M0HID/Keyboard/pcb/CherryMX-master/r3/r3_200.STEP

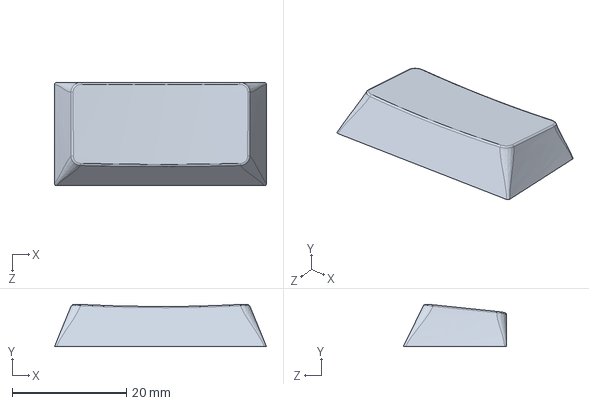
[picture p16: CAD file, 2025-07-31]
pcb/CherryMX-master/r3/r3_200.STEP
37.1 x 7.40 x 18.1 mm
