M0HID/Keyboard/pcb/CherryMX-master/r4/r4_225C.step

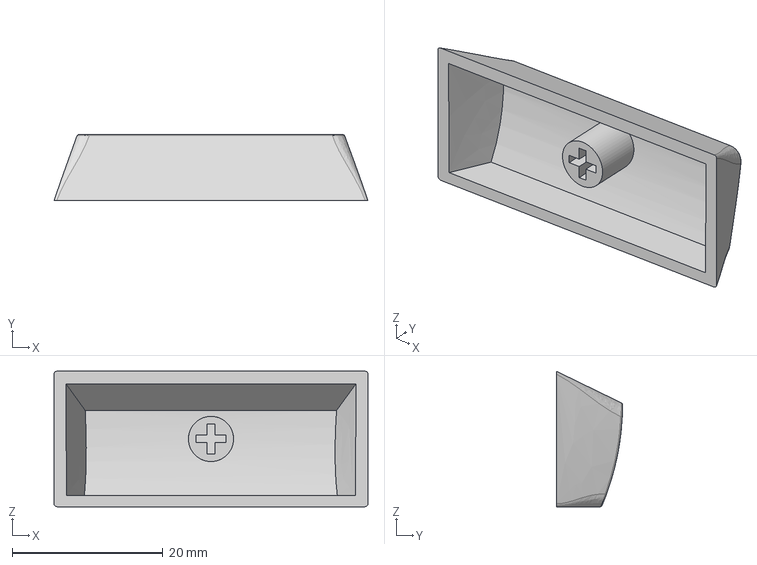
[picture p17: CAD file, 2025-07-31]
pcb/CherryMX-master/r4/r4_225C.step
41.7 x 8.80 x 18.0 mm
