M0HID/Keyboard/PROD/bottomshell.stl

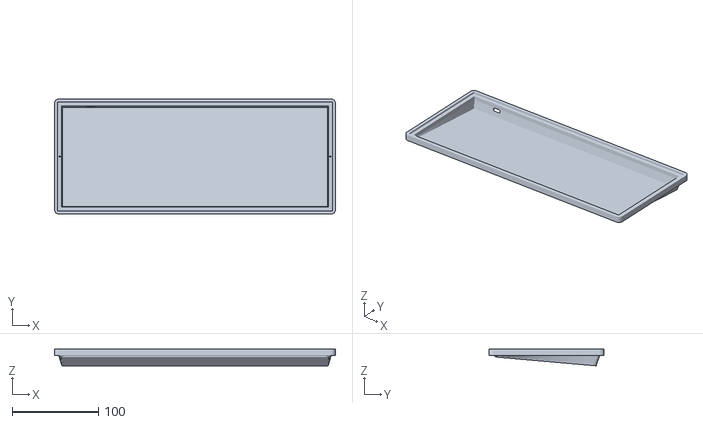
[picture p18: CAD file, 2025-07-31]
PROD/bottomshell.stl
326.0 x 133.6 x 19.4
