M0HID/Keyboard/pcb/CherryMX-master/r3/r3_150.STEP

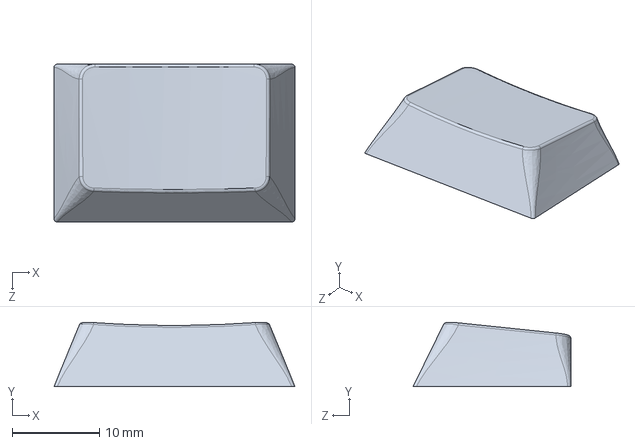
[picture p19: CAD file, 2025-07-31]
pcb/CherryMX-master/r3/r3_150.STEP
27.6 x 7.38 x 18.1 mm
