M0HID/Keyboard/pcb/CherryMX-master/r4/r4_100.STEP

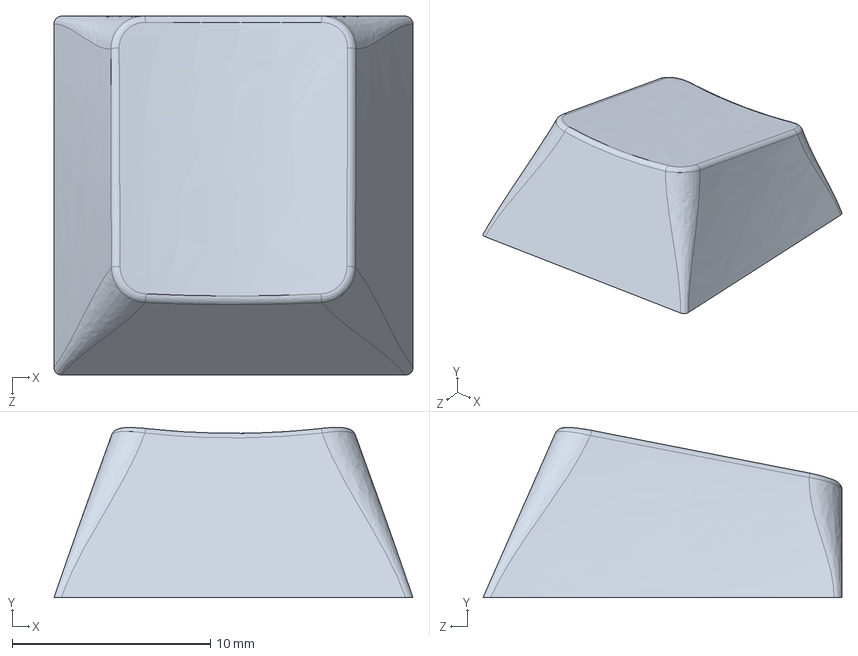
[picture p20: CAD file, 2025-07-31]
pcb/CherryMX-master/r4/r4_100.STEP
18.1 x 8.58 x 18.1 mm
