M0HID/Keyboard/pcb/CherryMX-master/r3/r3_100_sculpted.STEP

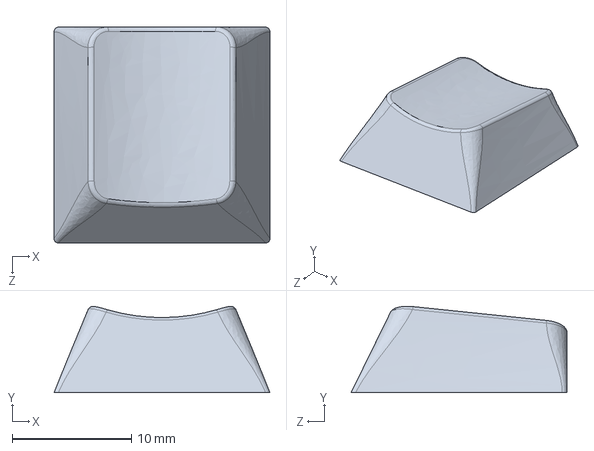
[picture p21: CAD file, 2025-07-31]
pcb/CherryMX-master/r3/r3_100_sculpted.STEP
18.1 x 7.24 x 18.1 mm
