M0HID/Keyboard/pcb/CherryMX-master/r4/r4_700.STEP

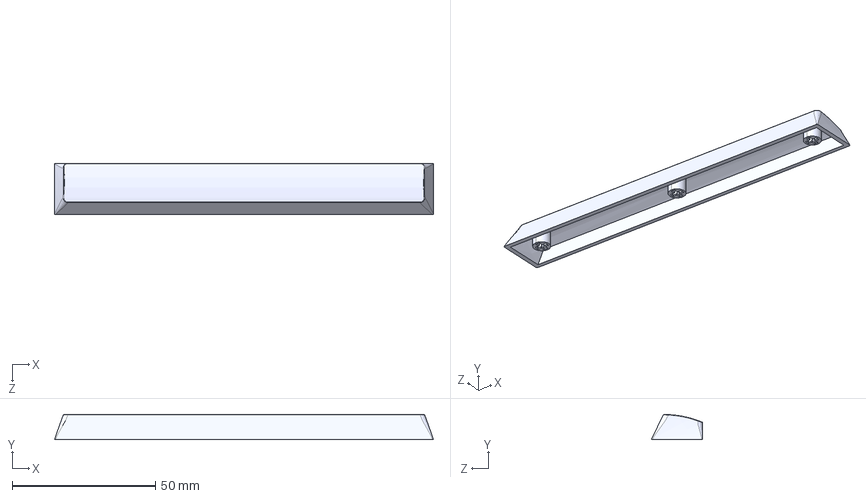
[picture p22: CAD file, 2025-07-31]
pcb/CherryMX-master/r4/r4_700.STEP
132.5 x 8.80 x 18.0 mm
