M0HID/Keyboard/pcb/CherryMX-master/r3/r3_100_bar.STEP

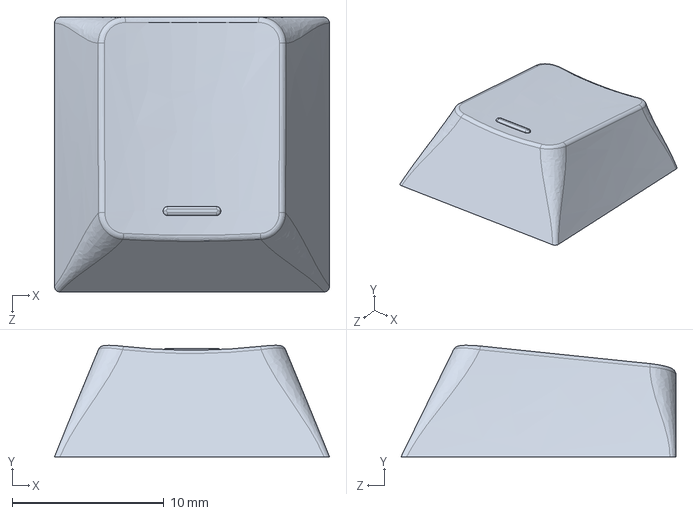
[picture p23: CAD file, 2025-07-31]
pcb/CherryMX-master/r3/r3_100_bar.STEP
18.1 x 7.34 x 18.1 mm
