M0HID/Keyboard/pcb/CherryMX-master/r4/r4_200C.step

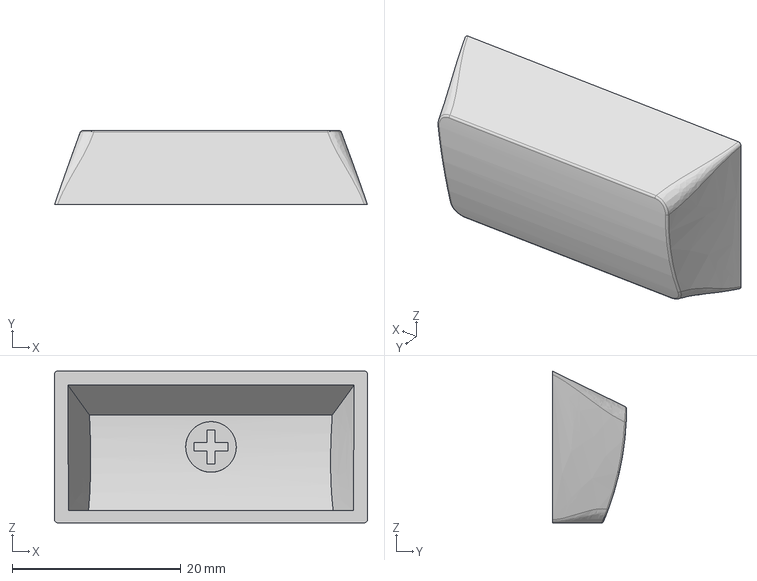
[picture p24: CAD file, 2025-07-31]
pcb/CherryMX-master/r4/r4_200C.step
37.1 x 8.80 x 18.0 mm
