M0HID/Keyboard/pcb/CherryMX-master/r3/r3_175_stepped.STEP

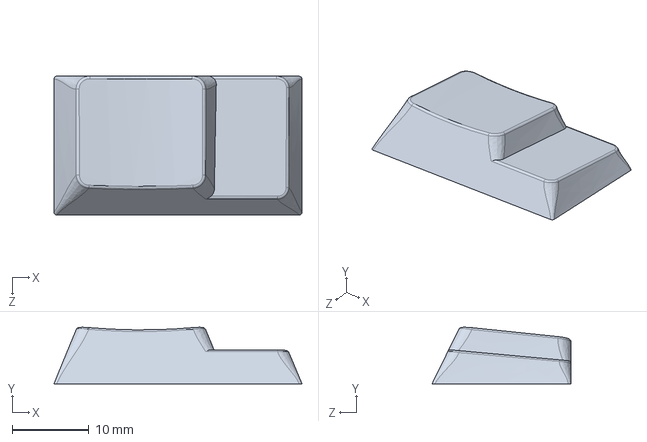
[picture p25: CAD file, 2025-07-31]
pcb/CherryMX-master/r3/r3_175_stepped.STEP
32.3 x 7.36 x 18.1 mm
