M0HID/Keyboard/pcb/CherryMX-master/r4/r4_300C.step

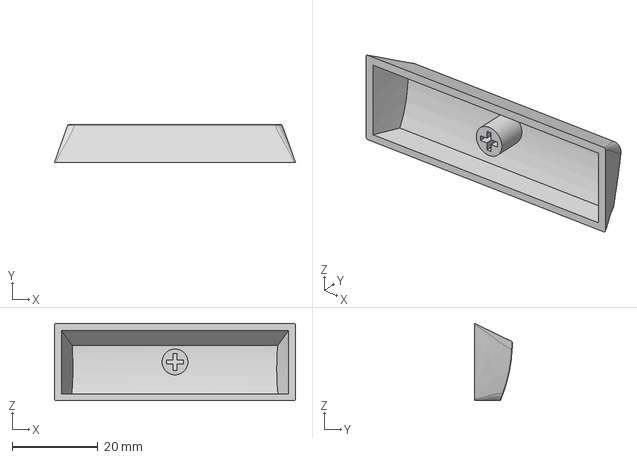
[picture p26: CAD file, 2025-07-31]
pcb/CherryMX-master/r4/r4_300C.step
56.1 x 8.80 x 18.0 mm
