M0HID/Keyboard/pcb/CherryMX-master/r4/r3-4_200vert.STEP

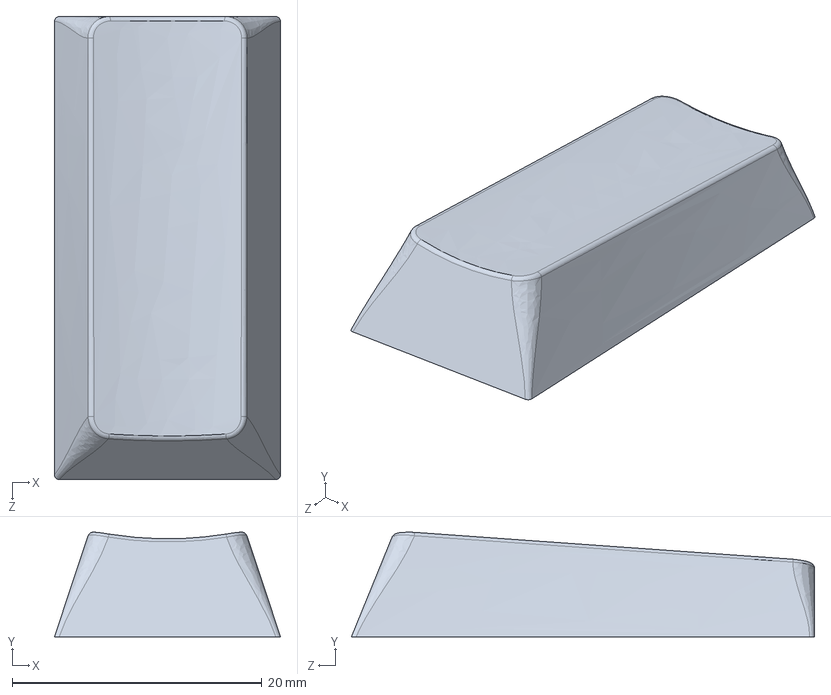
[picture p27: CAD file, 2025-07-31]
pcb/CherryMX-master/r4/r3-4_200vert.STEP
18.1 x 8.38 x 37.1 mm
