M0HID/Keyboard/pcb/CherryMX-master/r3/r3_iso.STEP

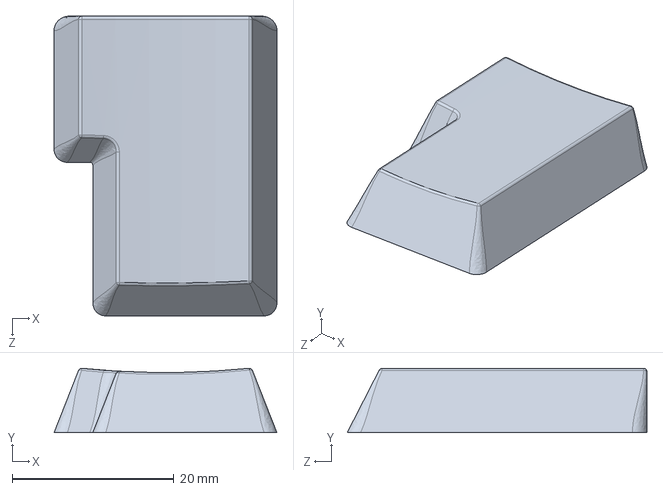
[picture p28: CAD file, 2025-07-31]
pcb/CherryMX-master/r3/r3_iso.STEP
27.6 x 7.97 x 37.1 mm
