M0HID/Keyboard/pcb/CherryMX-master/r4/r4_100C.step

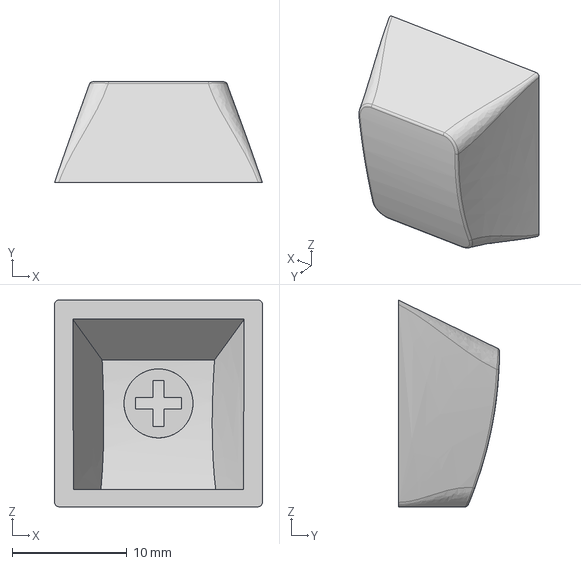
[picture p29: CAD file, 2025-07-31]
pcb/CherryMX-master/r4/r4_100C.step
18.1 x 8.80 x 18.0 mm
