M0HID/Keyboard/pcb/CherryMX-master/r3/r3_225.STEP

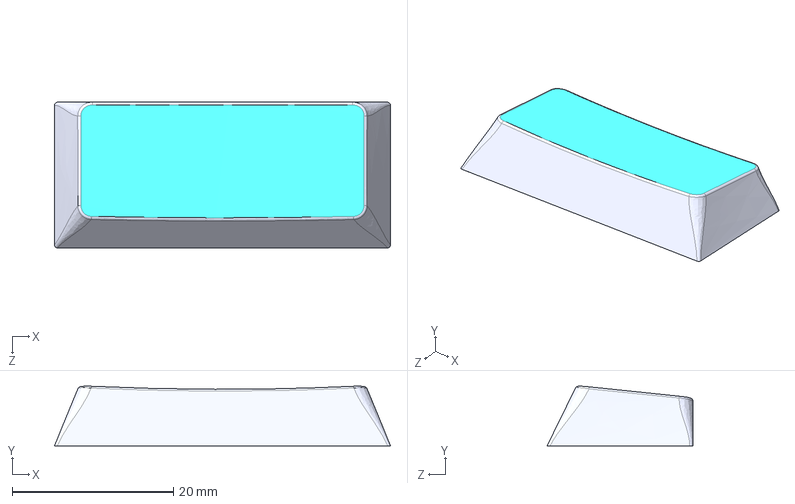
[picture p30: CAD file, 2025-07-31]
pcb/CherryMX-master/r3/r3_225.STEP
41.7 x 7.41 x 18.1 mm
