M0HID/Keyboard/pcb/CherryMX-master/r4/r4_150.STEP

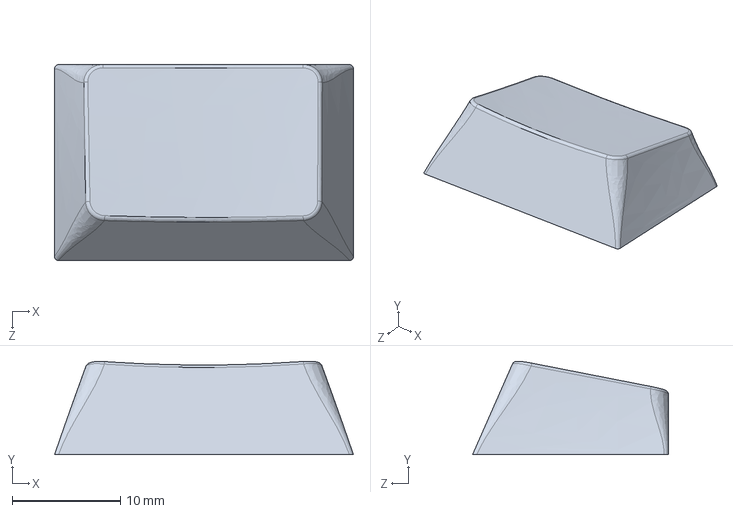
[picture p31: CAD file, 2025-07-31]
pcb/CherryMX-master/r4/r4_150.STEP
27.6 x 8.63 x 18.1 mm
