M0HID/Keyboard/pcb/CherryMX-master/r3/r3_175.STEP

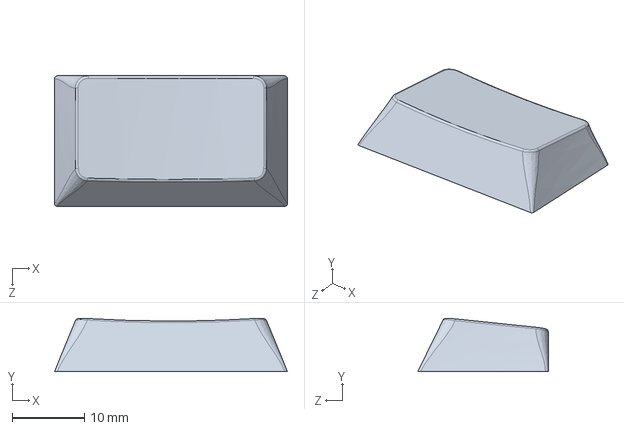
[picture p32: CAD file, 2025-07-31]
pcb/CherryMX-master/r3/r3_175.STEP
32.3 x 7.39 x 18.1 mm
