M0HID/Keyboard/pcb/CherryMX-master/r4/r4_625.STEP

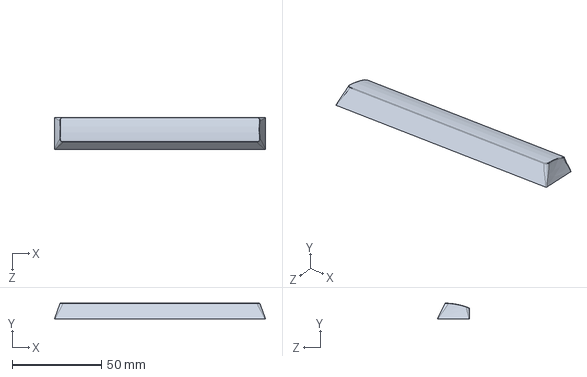
[picture p33: CAD file, 2025-07-31]
pcb/CherryMX-master/r4/r4_625.STEP
118.1 x 8.80 x 18.0 mm
