M0HID/Keyboard/pcb/CherryMX-master/r4/r4_175.STEP

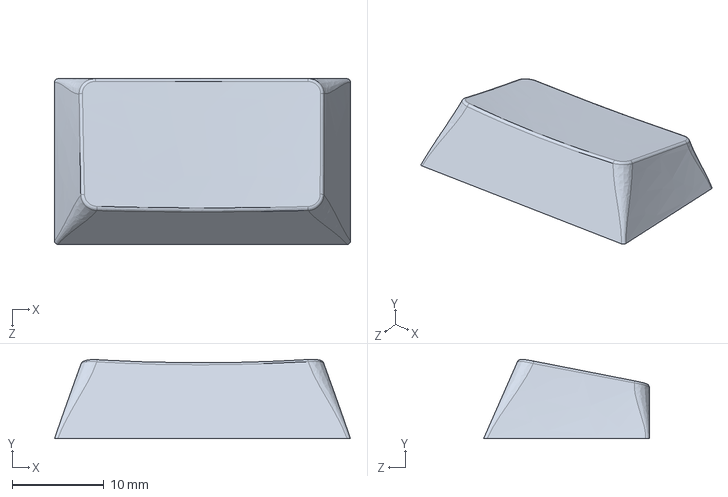
[picture p34: CAD file, 2025-07-31]
pcb/CherryMX-master/r4/r4_175.STEP
32.3 x 8.65 x 18.1 mm
