M0HID/Keyboard/pcb/CherryMX-master/r4/r4_125.STEP

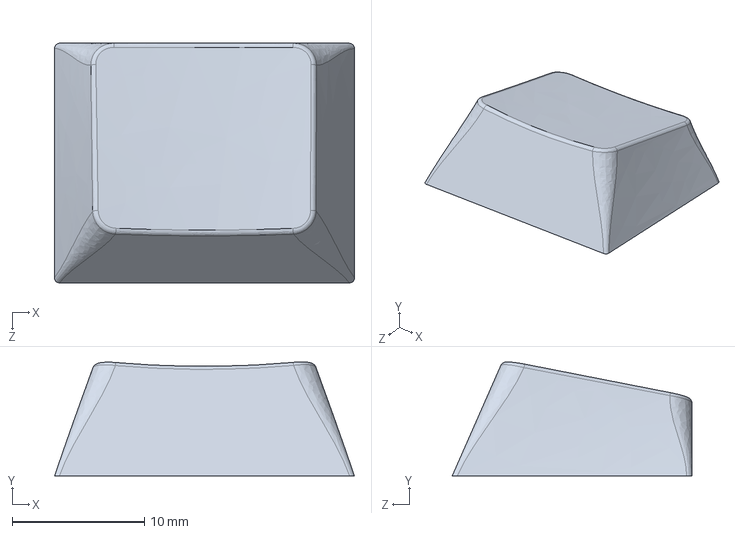
[picture p35: CAD file, 2025-07-31]
pcb/CherryMX-master/r4/r4_125.STEP
22.7 x 8.61 x 18.1 mm
