M0HID/Keyboard/pcb/CherryMX-master/r4/r4_275.STEP

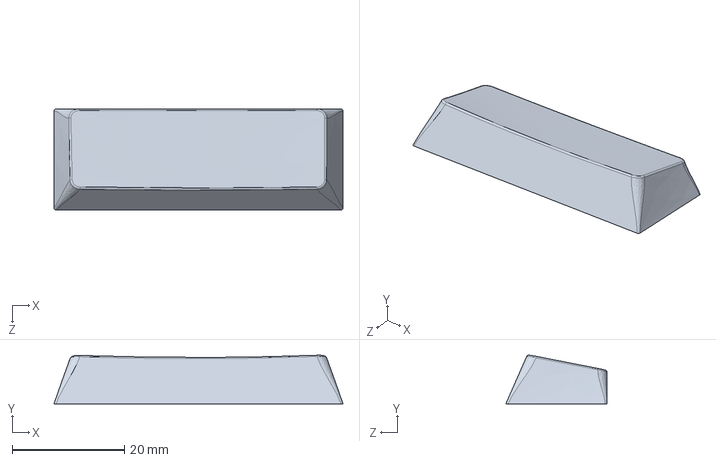
[picture p36: CAD file, 2025-07-31]
pcb/CherryMX-master/r4/r4_275.STEP
51.6 x 8.69 x 18.1 mm
