M0HID/Keyboard/pcb/CherryMX-master/r4/r4_175C.step

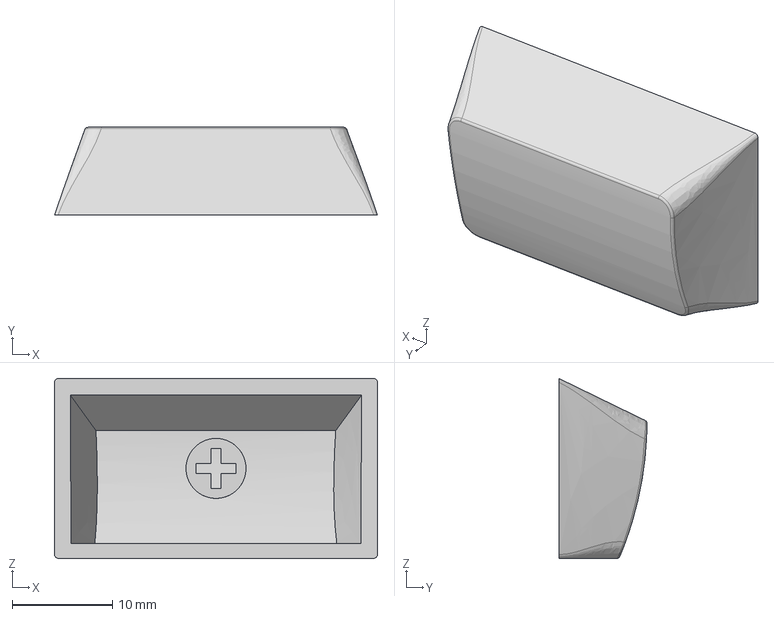
[picture p37: CAD file, 2025-07-31]
pcb/CherryMX-master/r4/r4_175C.step
32.3 x 8.80 x 18.0 mm
