M0HID/Keyboard/pcb/CherryMX-master/r4/r4_200.STEP

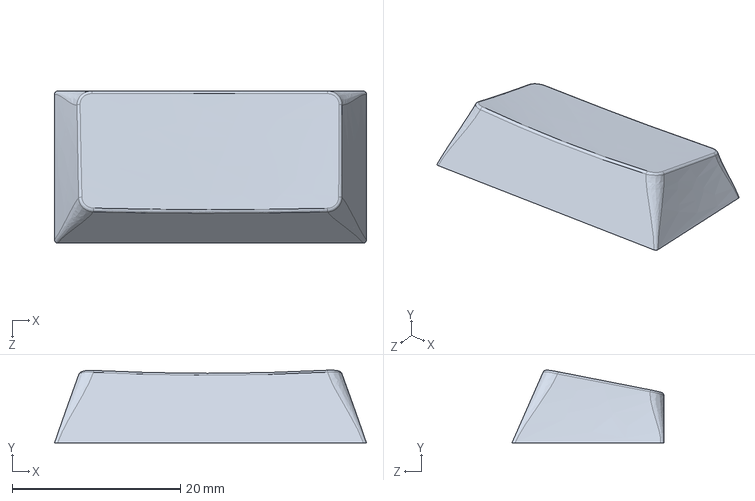
[picture p38: CAD file, 2025-07-31]
pcb/CherryMX-master/r4/r4_200.STEP
37.1 x 8.66 x 18.1 mm
