M0HID/Keyboard/pcb/CherryMX-master/r4/r4_225.STEP

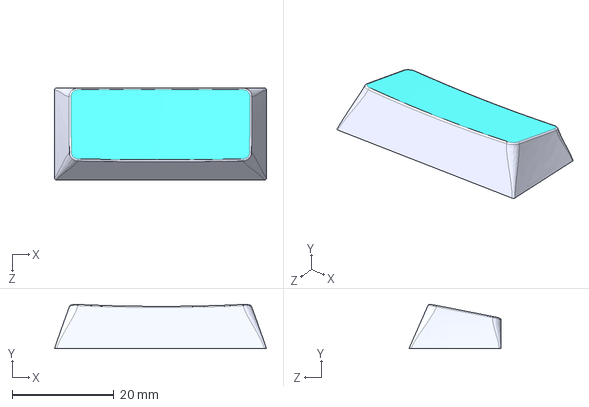
[picture p39: CAD file, 2025-07-31]
pcb/CherryMX-master/r4/r4_225.STEP
41.7 x 8.67 x 18.1 mm
